qistoph/BedLed/src/buttons.cpp

#include "buttons.h"

void buttonsSetup() {
  pinMode(BTN1_PIN, INPUT_PULLUP);
  pinMode(BTN2_PIN, INPUT_PULLUP);
}

unsigned long lastDebounceTime[2] = {0, 0};
int buttonState[2] = {HIGH, HIGH};
int lastButtonState[2] = { HIGH, HIGH }; // Using internal pull-up, so default high

void updateButtonState(uint8_t pin, uint8_t index) {
  int reading = digitalRead(pin);

  //Serial.print("Pin ");
  //Serial.print(pin);
  //Serial.print(": ");
  //Serial.println(reading);

  if (reading != lastButtonState[index]) {
    lastDebounceTime[index] = millis();
    lastButtonState[index] = reading;
  }

  //Serial.println(millis());
  //Serial.println(lastDebounceTime[index]);
  //Serial.println(DEBOUNCE_DELAY);

  if ((millis() - lastDebounceTime[index]) > DEBOUNCE_DELAY) {
    buttonState[index] = reading;
  }
}

uint8_t buttonsReadTouch() {
  updateButtonState(BTN1_PIN, 0);
  updateButtonState(BTN2_PIN, 1);

  //Serial.print("\rButtons: ");
  //Serial.print(buttonState[0]);
  //Serial.print(", ");
  //Serial.print(buttonState[1]);

  // Using internal pull-up, so LOW means touch
  // 0 - Non pressed
  // 1 - BTN1 pressed
  // 2 - BTN2 pressed
  // 3 - BTN1 and BTN2 pressed
  return ((buttonState[0] == LOW) ? 1 : 0) | ((buttonState[1] == LOW) ? 2 : 0);
}
